bmoren/INT-EXP/examples/openFrameworks/openframeworks-basic/src/ofApp.cpp

#include "ofApp.h"

//--------------------------------------------------------------
void ofApp::setup(){

}

//--------------------------------------------------------------
void ofApp::update(){

}

//--------------------------------------------------------------
void ofApp::draw(){

}

//--------------------------------------------------------------
void ofApp::keyPressed(int key){
    if (key == 'a'){
        ofLog(OF_LOG_NOTICE, "the a key was pressed in the keyPressed Function" );
    }

}

//--------------------------------------------------------------
void ofApp::keyReleased(int key){
    if (key == 'a'){
        ofLog(OF_LOG_NOTICE, "the a key was released in the keyPressed Function" );
    }

}

//--------------------------------------------------------------
void ofApp::mouseMoved(int x, int y ){

}

//--------------------------------------------------------------
void ofApp::mouseDragged(int x, int y, int button){

}

//--------------------------------------------------------------
void ofApp::mousePressed(int x, int y, int button){

}

//--------------------------------------------------------------
void ofApp::mouseReleased(int x, int y, int button){

}

//--------------------------------------------------------------
void ofApp::mouseEntered(int x, int y){

}

//--------------------------------------------------------------
void ofApp::mouseExited(int x, int y){

}

//--------------------------------------------------------------
void ofApp::windowResized(int w, int h){

}

//--------------------------------------------------------------
void ofApp::gotMessage(ofMessage msg){

}

//--------------------------------------------------------------
void ofApp::dragEvent(ofDragInfo dragInfo){ 

}
